stdevPavelmc/awrc/doc/freeing up GPIO9 and GPIO10 smarpl.com_files/ESP8266-ESP-201-GPIO-mod-step2-IMG_7927.jpg

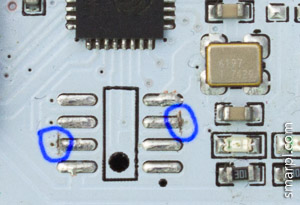
doc/freeing up GPIO9 and GPIO10 smarpl.com_files/ESP8266-ESP-201-GPIO-mod-step2-IMG_7927.jpg
