stdevPavelmc/awrc/doc/freeing up GPIO9 and GPIO10 smarpl.com_files/ESP8266-ESP-201-GPIO-mod-step4-IMG_7932.jpg

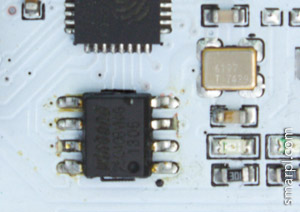
doc/freeing up GPIO9 and GPIO10 smarpl.com_files/ESP8266-ESP-201-GPIO-mod-step4-IMG_7932.jpg
